alsav/stm8-soldering-station-controller/IMG1.jpg

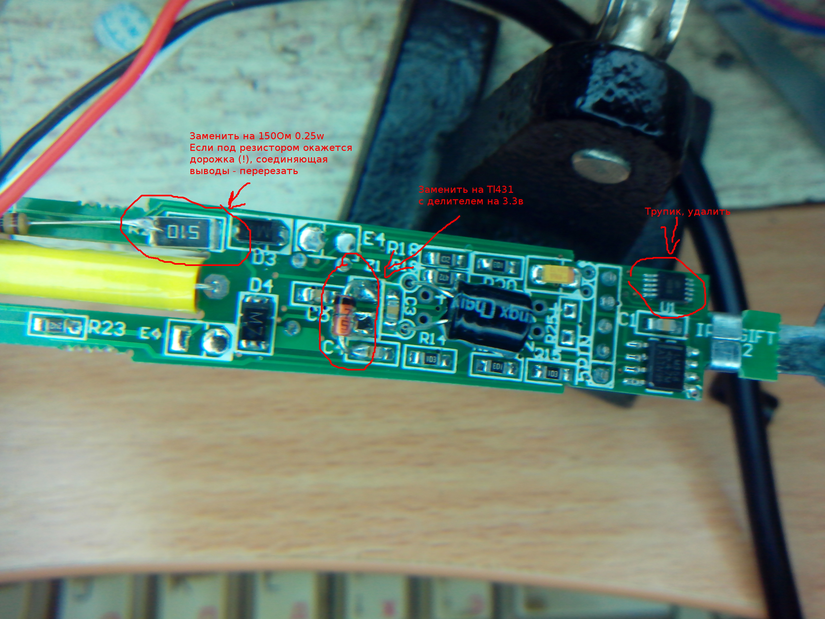
IMG1.jpg
