alsav/stm8-soldering-station-controller/IMG4.jpg

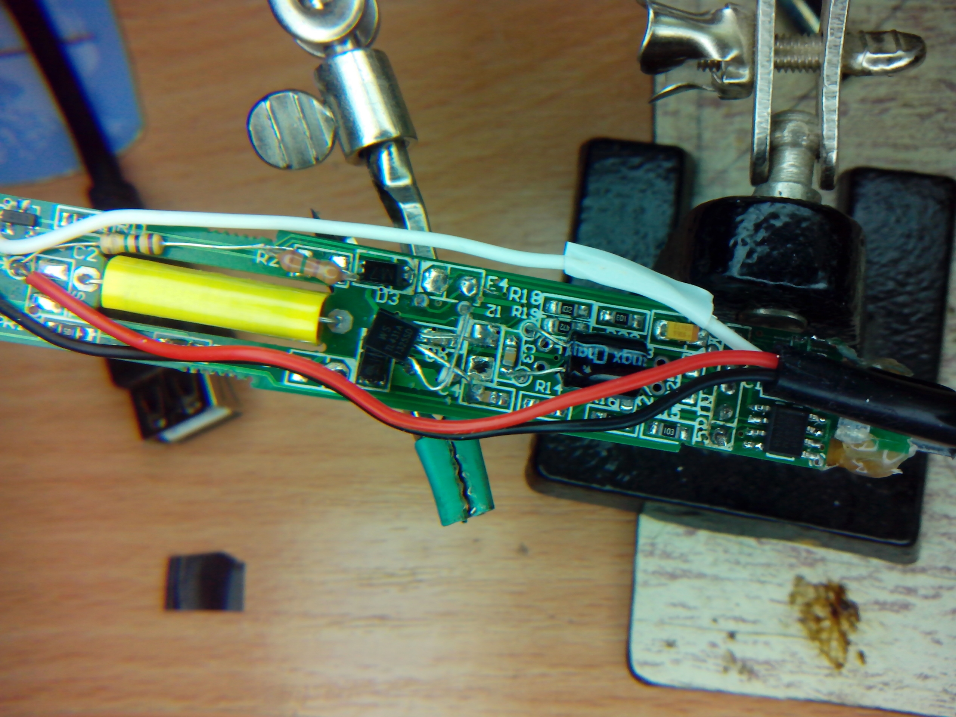
IMG4.jpg
